Flanker-E/All_In_One_Outdoor_Sports_Comupter/.assets/GUI.png

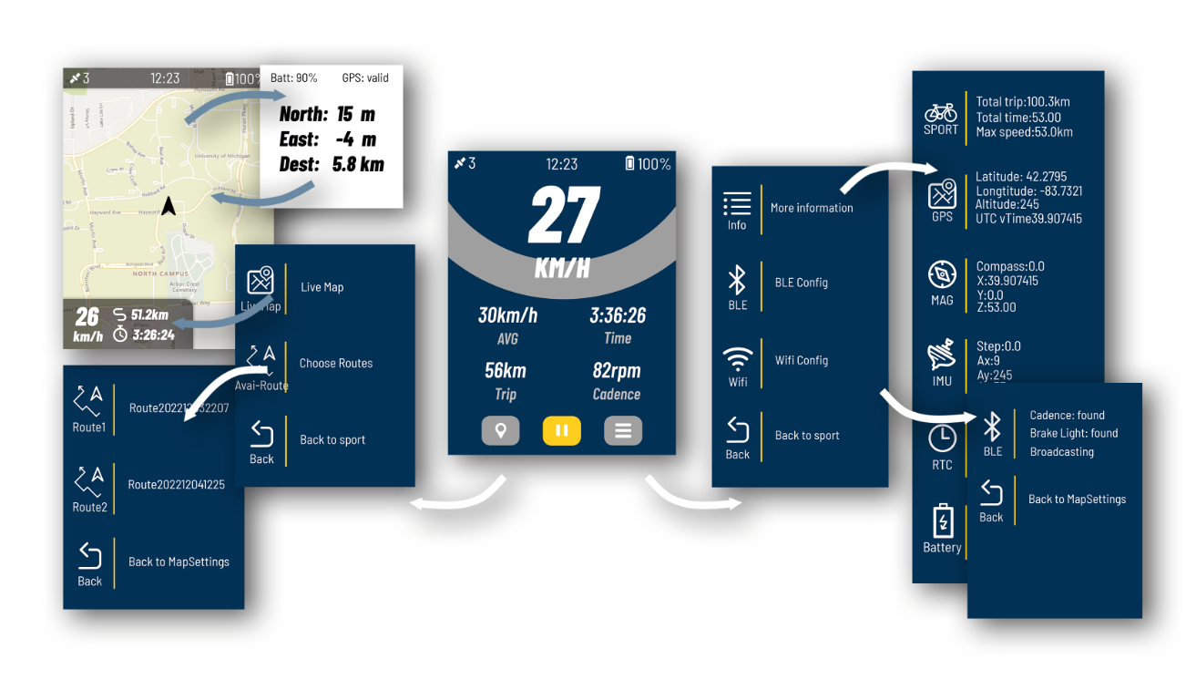
.assets/GUI.png
