Flanker-E/All_In_One_Outdoor_Sports_Comupter/.assets/introduction.png

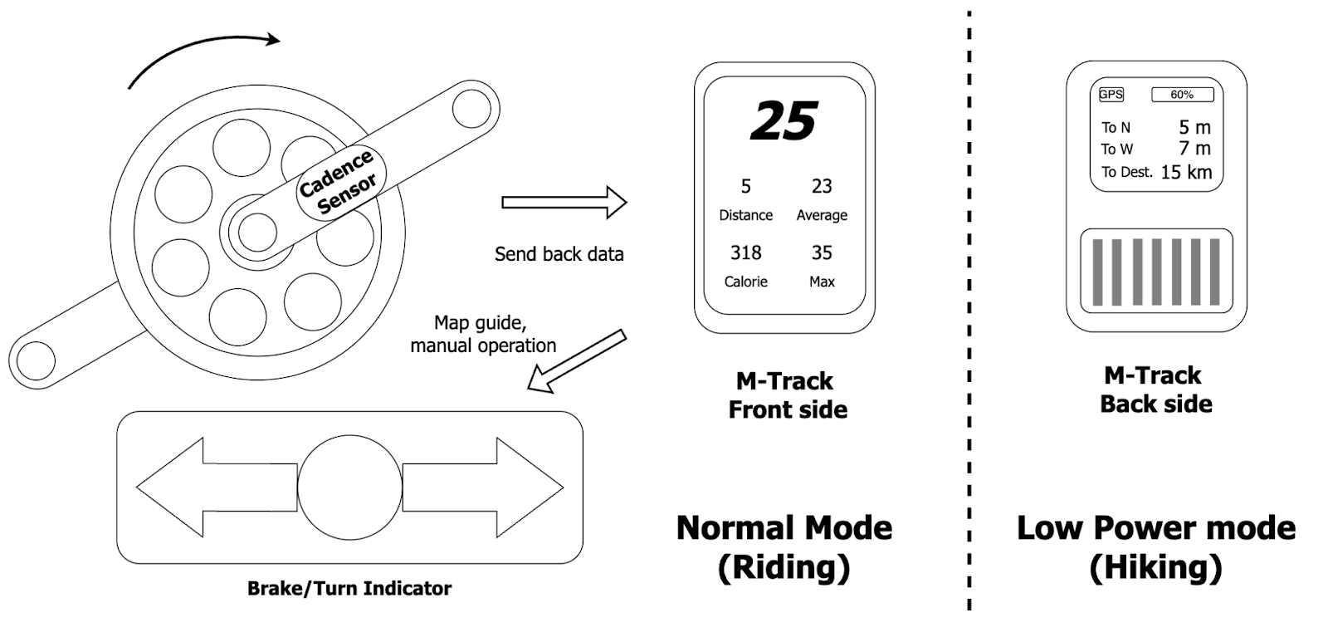
.assets/introduction.png
