Flanker-E/All_In_One_Outdoor_Sports_Comupter/Poster/All PCBs.png

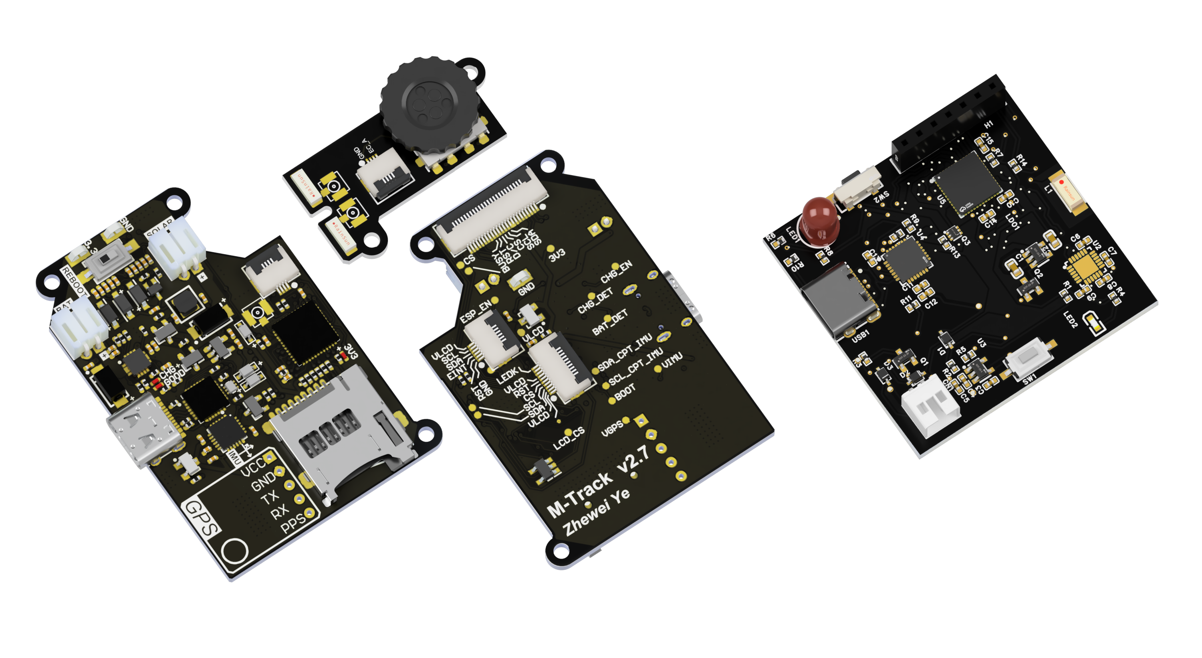
Poster/All PCBs.png
