Flanker-E/All_In_One_Outdoor_Sports_Comupter/Poster/Bike Computer Software Arch.png

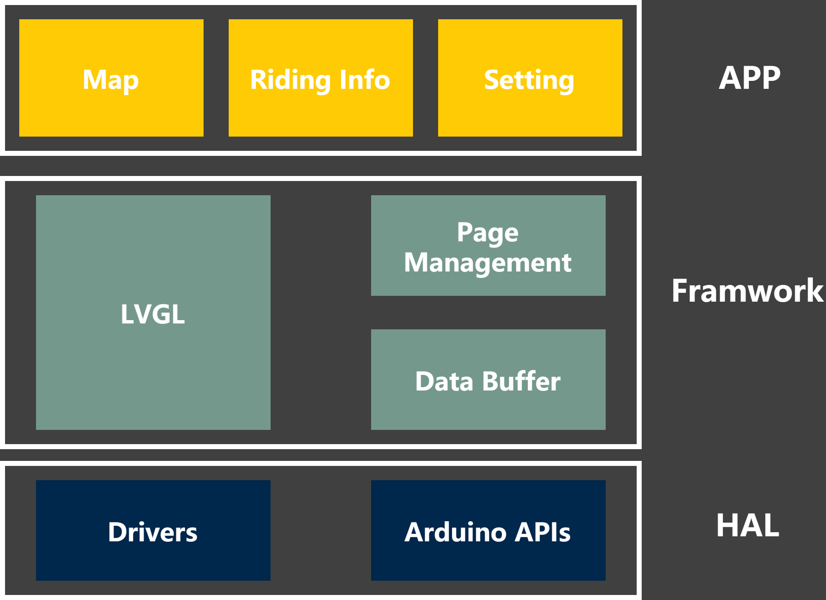
Poster/Bike Computer Software Arch.png
