Flanker-E/All_In_One_Outdoor_Sports_Comupter/Poster/Bike Computer System.png

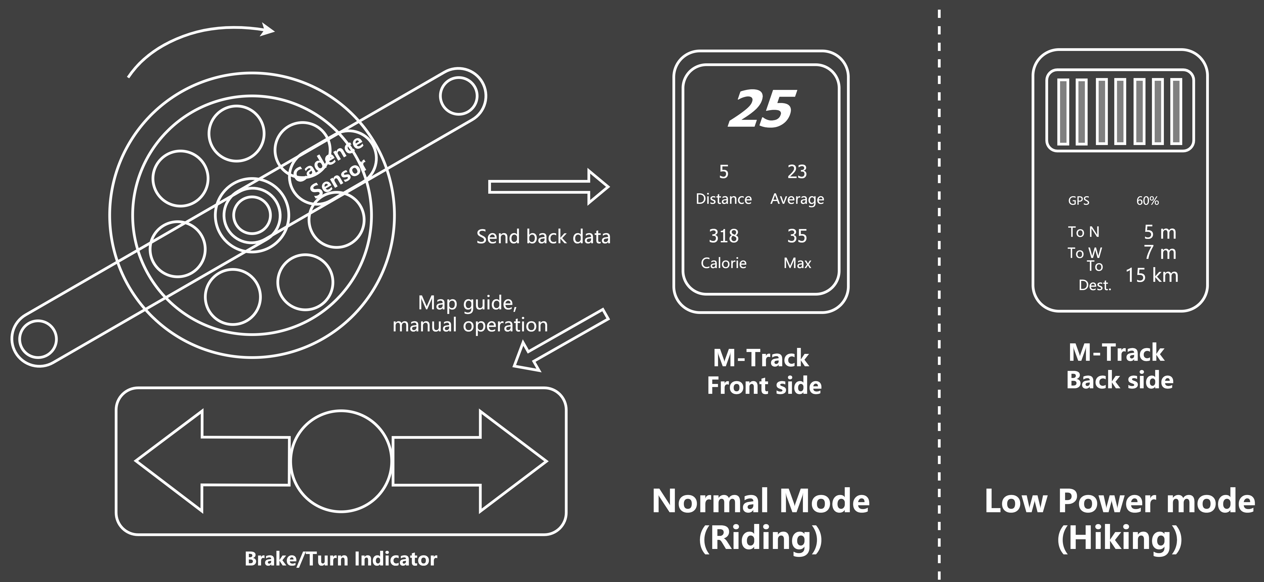
Poster/Bike Computer System.png
