Flanker-E/All_In_One_Outdoor_Sports_Comupter/src/App/Pages/Dialplate/Dialplate.cpp

#include "Dialplate.h"
#include "../../Utils/PageManager/PM_Log.h"
#ifdef ARDUINO
#  include "Arduino.h"
#endif

using namespace Page;

Dialplate::Dialplate()
    : recState(RECORD_STATE_READY)
    , lastFocus(nullptr)
{
}

Dialplate::~Dialplate()
{
}

void Dialplate::onCustomAttrConfig()
{
    SetCustomLoadAnimType(PageManager::LOAD_ANIM_NONE);
}

void Dialplate::onViewLoad()
{
    // Serial.println("Init start");
    Model.Init();
    // Serial.println("model Init");
    View.Create(root);

    AttachEvent(View.ui.btnCont.btnMap);
    AttachEvent(View.ui.btnCont.btnRec);
    AttachEvent(View.ui.btnCont.btnMenu);
    PM_LOG_DEBUG_LN("Init done");
}

void Dialplate::onViewDidLoad()
{

}

void Dialplate::onViewWillAppear()
{
    //Serial.println("onviewwillappear");
    lv_indev_wait_release(lv_indev_get_act());
    //Serial.println("onviewwillappear");
    lv_group_t* group = lv_group_get_default();
    //Serial.println("onviewwillappear");
    lv_group_set_wrap(group, false);
    //Serial.println("addobj");
    lv_group_add_obj(group, View.ui.btnCont.btnMap);
    //Serial.println("btnMap");
    lv_group_add_obj(group, View.ui.btnCont.btnRec);
    //Serial.println("btnRec");
    lv_group_add_obj(group, View.ui.btnCont.btnMenu);
    //Serial.println("btnMenu");

    if (lastFocus)
    {
        lv_group_focus_obj(lastFocus);
    }
    else
    {
        lv_group_focus_obj(View.ui.btnCont.btnRec);
    }
    //Serial.println("group");
    Model.SetStatusBarStyle(DataProc::STATUS_BAR_STYLE_TRANSP);
    //Serial.println("to update");
    Update();

    View.AppearAnimStart();
}

void Dialplate::onViewDidAppear()
{
    timer = lv_timer_create(onTimerUpdate, 1000, this);
}

void Dialplate::onViewWillDisappear()
{
    lv_group_t* group = lv_group_get_default();
    lastFocus = lv_group_get_focused(group);
    lv_group_remove_all_objs(group);
    lv_timer_del(timer);
    //View.AppearAnimStart(true);
}

void Dialplate::onViewDidDisappear()
{
}

void Dialplate::onViewDidUnload()
{
    Model.Deinit();
    View.Delete();
}

void Dialplate::AttachEvent(lv_obj_t* obj)
{
    lv_obj_add_event_cb(obj, onEvent, LV_EVENT_ALL, this);
}

void Dialplate::Update()
{
    // Serial.println("update");
    char buf[16];
    lv_label_set_text_fmt(View.ui.topInfo.labelSpeed, "%02d", (int)Model.GetSpeed());
    // Serial.println("update");

    lv_label_set_text_fmt(View.ui.bottomInfo.labelInfoGrp[0].lableValue, "%0.1f km/h", Model.GetAvgSpeed());
    lv_label_set_text(
        View.ui.bottomInfo.labelInfoGrp[1].lableValue,
        DataProc::MakeTimeString(Model.sportStatusInfo.singleTime, buf, sizeof(buf))
    );
    // Serial.println("update");
    
    lv_label_set_text_fmt(
        View.ui.bottomInfo.labelInfoGrp[2].lableValue,
        "%0.1f km",
        Model.sportStatusInfo.singleDistance / 1000
    );
    // Serial.println("update");

    lv_label_set_text_fmt(
        View.ui.bottomInfo.labelInfoGrp[3].lableValue,
        "%d k",
        int(Model.sportStatusInfo.singleCalorie)
    );
    // Serial.println("updated");
}

void Dialplate::onTimerUpdate(lv_timer_t* timer)
{
    Dialplate* instance = (Dialplate*)timer->user_data;

    instance->Update();
}

void Dialplate::onBtnClicked(lv_obj_t* btn)
{
    if (btn == View.ui.btnCont.btnMap)
    {
        Manager->Push("Pages/MapSettings");
        PM_LOG_DEBUG_LN("MapSettings");
        
    }
    else if (btn == View.ui.btnCont.btnMenu)
    {
        Manager->Push("Pages/Settings");
        PM_LOG_DEBUG_LN("settings");
    }
}

void Dialplate::onRecord(bool longPress)
{
    switch (recState)
    {
    case RECORD_STATE_READY:
        if (longPress)
        {
            if (!Model.GetGPSReady())
            {
                PM_LOG_WARN("GPS has not ready, can't start record");
                // Model.PlayMusic("Error");
                return;
            }
            PM_LOG_INFO("record state start");
            // Model.PlayMusic("Connect");
            Model.RecorderCommand(Model.REC_START);
            SetBtnRecImgSrc("pause");
            recState = RECORD_STATE_RUN;
        }
        break;
    case RECORD_STATE_RUN:
        if (!longPress)
        {
            PM_LOG_INFO("record state pause");
            // Model.PlayMusic("UnstableConnect");
            Model.RecorderCommand(Model.REC_PAUSE);
            SetBtnRecImgSrc("start");
            recState = RECORD_STATE_PAUSE;
        }
        break;
    case RECORD_STATE_PAUSE:
        if (longPress)
        {
            PM_LOG_INFO("record state stop");
            // Model.PlayMusic("NoOperationWarning");
            SetBtnRecImgSrc("stop");
            Model.RecorderCommand(Model.REC_READY_STOP);
            recState = RECORD_STATE_STOP;
        }
        else
        {
            PM_LOG_INFO("record state restart");
            // Model.PlayMusic("Connect");
            Model.RecorderCommand(Model.REC_CONTINUE);
            SetBtnRecImgSrc("pause");
            recState = RECORD_STATE_RUN;
        }
        break;
    case RECORD_STATE_STOP:
        if (longPress)
        {
            PM_LOG_INFO("record state ready");
            // Model.PlayMusic("Disconnect");
            Model.RecorderCommand(Model.REC_STOP);
            SetBtnRecImgSrc("start");
            recState = RECORD_STATE_READY;
        }
        else
        {
            PM_LOG_INFO("record state pause");
            // Model.PlayMusic("Connect");
            Model.RecorderCommand(Model.REC_CONTINUE);
            SetBtnRecImgSrc("pause");
            recState = RECORD_STATE_RUN;
        }
        break;
    default:
        break;
    }
}

void Dialplate::SetBtnRecImgSrc(const char* srcName)
{
    lv_obj_set_style_bg_img_src(View.ui.btnCont.btnRec, ResourcePool::GetImage(srcName), 0);
}

void Dialplate::onEvent(lv_event_t* event)
{
    // instance is this here
    Dialplate* instance = (Dialplate*)lv_event_get_user_data(event);
    LV_ASSERT_NULL(instance);

    lv_obj_t* obj = lv_event_get_current_target(event);
    lv_event_code_t code = lv_event_get_code(event);

    // Serial.println("onevent");
    // if (code == LV_EVENT_PRESSED)
	// {
    //     PM_LOG_DEBUG_LN("pressed");
	// }
    if (code == LV_EVENT_SHORT_CLICKED)
    {
        instance->onBtnClicked(obj);
    }
    if (code == LV_EVENT_SHORT_CLICKED)
    {
        instance->onBtnClicked(obj);
    }

    if (obj == instance->View.ui.btnCont.btnRec)
    {
        if (code == LV_EVENT_SHORT_CLICKED)
        {
            instance->onRecord(false);
        }
        else if (code == LV_EVENT_LONG_PRESSED)
        {
            PM_LOG_DEBUG_LN("long pressed");
            instance->onRecord(true);
        }
        // keep pressing
        // else if (code == LV_EVENT_LONG_PRESSED_REPEAT){
        //     PM_LOG_DEBUG_LN("long pressed repeat");
        //     instance->onRecord(true);
        // }
    }
}
