Flanker-E/All_In_One_Outdoor_Sports_Comupter/src/HAL/HAL.h

#ifndef __HAL_H
#define __HAL_H

#include <stdint.h>
#include <Arduino.h>
#include "HAL_Def.h"
#include "App/Configs/Config.h"
#include "CommonMacro.h"
#include "M5Touch.h"
#include "TinyGPSPlus.h"
// #include "FreeRTOS.h"
#define HAVE_PERI 0

extern TinyGPSPlus gps;

namespace HAL
{

    typedef bool (*CommitFunc_t)(void* info, void* userData);

    void HAL_Init();
    void HAL_Update();

/* Backlight */
    void Backlight_Init();
    uint32_t Backlight_GetValue();
    void Backlight_SetValue(int32_t val);
    void Backlight_SetGradual(uint32_t target, uint16_t time = 500);
    void Backlight_ForceLit(bool en);

    /* Touch screen */
    void Touch_Init();
    bool Touch_Ispressed();
    void Touch_GetPressPoint(TouchPoint_t* coordinate);

/* I2C */
    void I2C_Init(bool startScan);

/* IMU */
    bool IMU_Init();
    void IMU_SetCommitCallback(CommitFunc_t func, void* userData);
    void IMU_Update();

/* MAG */
    bool MAG_Init();
    void MAG_SetCommitCallback(CommitFunc_t func, void* userData);
    void MAG_Update();

/* SD */
    bool SD_Init();
    void SD_Update();
    bool SD_GetReady();
    float SD_GetCardSizeMB();
    const char* SD_GetTypeName();
    typedef void(* SD_CallbackFunction_t)(bool insert);
    void SD_SetEventCallback(SD_CallbackFunction_t callback);

    bool BluetoothConnected();

/* Power */
    void Power_Init();
    void Power_HandleTimeUpdate();
    void Power_SetAutoLowPowerTimeout(uint16_t sec);
    uint16_t Power_GetAutoLowPowerTimeout();
    void Power_SetAutoLowPowerEnable(bool en);
    void Power_Shutdown();
    void Power_Update();
    void Power_EventMonitor();
    void Power_GetInfo(Power_Info_t* info);
    typedef void(* Power_CallbackFunction_t)(void);
    void Power_SetEventCallback(Power_CallbackFunction_t callback);

/* Clock */
    void Clock_Init();
    void Clock_GetInfo(Clock_Info_t* info);
    void Clock_SetInfo(const Clock_Info_t* info);
    const char* Clock_GetWeekString(uint8_t week);

/* GPS */
    void GPS_Init();
    void GPS_Update();
    bool GPS_GetInfo(GPS_Info_t* info);
    bool GPS_LocationIsValid();
    double GPS_GetDistanceOffset(GPS_Info_t* info, double preLong, double preLat);

/* Buzzer */
    void Buzz_init();
    void Buzz_SetEnable(bool en);
    void Buzz_Tone(uint32_t freq, int32_t duration = 0);

/* Encoder */
    void Encoder_Init();
    void Encoder_Update();
    int16_t Encoder_GetDiff();
    bool Encoder_GetIsPush();
    void Encoder_SetEnable(bool en);

/* Audio */
    void Audio_Init();
    void Audio_Update();
    bool Audio_PlayMusic(const char* name);


/* Bluetooth */
    bool BT_Init();
    void BT_Update();

/*Switches */
    void SW_Init();
    void LCD_On();
    void LCD_Off();
    void IMU_GPS_On();
    void IMU_GPS_Off();
    

}

#endif
