Flanker-E/All_In_One_Outdoor_Sports_Comupter/src/App/Pages/MapSettings/MapSettings.h

#ifndef __MAPSETTINGS_PRESENTER_H
#define __MAPSETTINGS_PRESENTER_H

#include "MapSettingsView.h"
#include "MapSettingsModel.h"

namespace Page
{

class MapSettings : public PageBase
{
public:

public:
    MapSettings();
    virtual ~MapSettings();

    virtual void onCustomAttrConfig();
    virtual void onViewLoad();
    virtual void onViewDidLoad();
    virtual void onViewWillAppear();
    virtual void onViewDidAppear();
    virtual void onViewWillDisappear();
    virtual void onViewDidDisappear();
    virtual void onViewDidUnload();

private:
    static void onTimer(lv_timer_t* timer);
    void Update();
    void AttachEvent(lv_obj_t* obj);
    static void onTimerUpdate(lv_timer_t* timer);
    static void onEvent(lv_event_t* event);
    void onBtnClicked(lv_obj_t* btn);

private:
    MapSettingsView View;
    MapSettingsModel Model;
    lv_timer_t* timer;
    lv_obj_t* lastFocus;
};

}

#endif
