Flanker-E/All_In_One_Outdoor_Sports_Comupter/src/Port/DIsplay.h

#ifndef __DISPLAY_H
#define __DISPLAY_H

#include <TFT_eSPI.h>
#include "App/Configs/Config.h"
#include "lvgl.h"
#include "FS.h"

// #include "TFT_eSPI.h"
typedef TFT_eSPI SCREEN_CLASS;
extern TFT_eSPI tft; /* TFT instance */
// TFT_eSPI tft = TFT_eSPI();
// int test=0;
// static lv_indev_drv_t indev_drv;
extern lv_indev_t* touch_indev;
extern lv_indev_t* encoder_indev;

// #define CS_PIN          9
#define TRANSFER_TO_EINK  digitalWrite(TFT_CS,HIGH);
#define TRANSFER_TO_LCD   digitalWrite(TFT_CS,LOW);

#define TURN_ON_LCD    digitalWrite(CONFIG_SCREEN_PWR_PIN,LOW);
#define TURN_OFF_LCD   digitalWrite(CONFIG_SCREEN_PWR_PIN,HIGH);

// static const uint16_t screenWidth  = 320;
// static const uint16_t screenHeight = 240;

// static lv_disp_draw_buf_t draw_buf;
// static lv_color_t buf[ screenWidth * 80 ];

// static lv_color_t lv_disp_buf_p[ CONFIG_SCREEN_BUFFER_SIZE ];
// static lv_disp_draw_buf_t disp_buf;
// static lv_disp_drv_t disp_drv;

// TFT_eSPI tft = TFT_eSPI(); /* TFT instance */
#define CALIBRATION_FILE "/TouchCalData1"

#define REPEAT_CAL false
// typedef TFT_eSPI SCREEN_CLASS;
void To_LCD_Port();
void To_Eink_Port();
void LCD_Power_On();
void LCD_Power_Off();
void Port_Init_Eink();
void Port_Init();
void End_spi_transaction();
void startFreeRtos();
void DisplayFault_Init(SCREEN_CLASS* scr);
void lv_port_disp_lcd_init(SCREEN_CLASS* scr);
void lv_port_disp_eink_init();
void lv_fs_if_init();
void lv_port_indev_init();

extern TaskHandle_t handleTaskLvgl;

#endif
