Flanker-E/All_In_One_Outdoor_Sports_Comupter/src/App/Pages/Settings/SettingsModel.cpp

#include "SettingsModel.h"
#include <stdio.h>

using namespace Page;

void SettingsModel::Init(){
    account = new Account("SystemInfosModel", DataProc::Center(), 0, this);
    account->Subscribe("StatusBar");
}

void SettingsModel::Deinit(){
    if (account)
    {
        delete account;
        account = nullptr;
    }
}

void SettingsModel::SetStatusBarStyle(DataProc::StatusBar_Style_t style)
{
    DataProc::StatusBar_Info_t info;
    DATA_PROC_INIT_STRUCT(info);

    info.cmd = DataProc::STATUS_BAR_CMD_SET_STYLE;
    info.param.style = style;

    account->Notify("StatusBar", &info, sizeof(info));
}
