Flanker-E/All_In_One_Outdoor_Sports_Comupter/src/App/Pages/_Template/TemplateView.cpp

#include "TemplateView.h"

using namespace Page;
// extern lv_indev_t* encoder_indev;
//extern lv_indev_t* touch_indev;
void TemplateView::Create(lv_obj_t* root)
{
	lv_obj_t* label = lv_label_create(root);
	lv_obj_set_style_text_font(label, &lv_font_montserrat_14, 0);
	lv_obj_set_style_text_color(label, lv_color_white(), 0);
	lv_obj_align(label, LV_ALIGN_TOP_MID, 0, 30);
	lv_label_set_text(label, "");
	ui.labelTitle = label;

	label = lv_label_create(root);
	lv_obj_set_style_text_font(label, &lv_font_montserrat_10, 0);
	lv_obj_set_style_text_color(label, lv_color_white(), 0);
	lv_label_set_text(label, "");
	lv_obj_align(label, LV_ALIGN_TOP_MID, 0, 50);
	ui.labelTick = label;

	lv_obj_t* img = lv_img_create(root);
	lv_img_set_src(img, ResourcePool::GetImage("arm"));
	lv_obj_center(img);
	ui.canvas = img;

	ui.group = lv_group_create();
	// lv_indev_set_group(lv_get_indev(LV_INDEV_TYPE_ENCODER), ui.group);

	// lv_indev_set_group(encoder_indev, ui.group);
	//lv_indev_set_group(touch_indev, ui.group);

	lv_group_add_obj(ui.group, ui.canvas);
	lv_group_add_obj(ui.group, ui.labelTitle);
	lv_group_focus_obj(ui.canvas);

}
