Flanker-E/All_In_One_Outdoor_Sports_Comupter/src/HAL/HAL_Audio.cpp

#include "HAL/HAL.h"
#include "App/Utils/TonePlayer/TonePlayer.h"
#include "lvgl.h"

static TonePlayer player;

#include "App/Utils/TonePlayer/MusicCode.h"

static void Tone_Callback(uint32_t freq, uint16_t volume)
{
    HAL::Buzz_Tone(freq);
}

void HAL::Audio_Init()
{
    player.SetCallback(Tone_Callback);
    Buzz_Tone(1000, 1000);
}

void HAL::Audio_Update()
{
    player.Update(lv_tick_get());
}

bool HAL::Audio_PlayMusic(const char* name)
{
    bool retval = false;
    for (int i = 0; i < sizeof(MusicList) / sizeof(MusicList[0]); i++)
    {
        if (strcmp(name, MusicList[i].name) == 0)
        {
            player.Play(MusicList[i].mc, MusicList[i].length);
            retval = true;
            break;
        }
    }
    return retval;
}
